kholia/HF-PA-v2/[Hans' Grounding + ESD Tip] Screenshot_2021-07-30_19-16-26.png

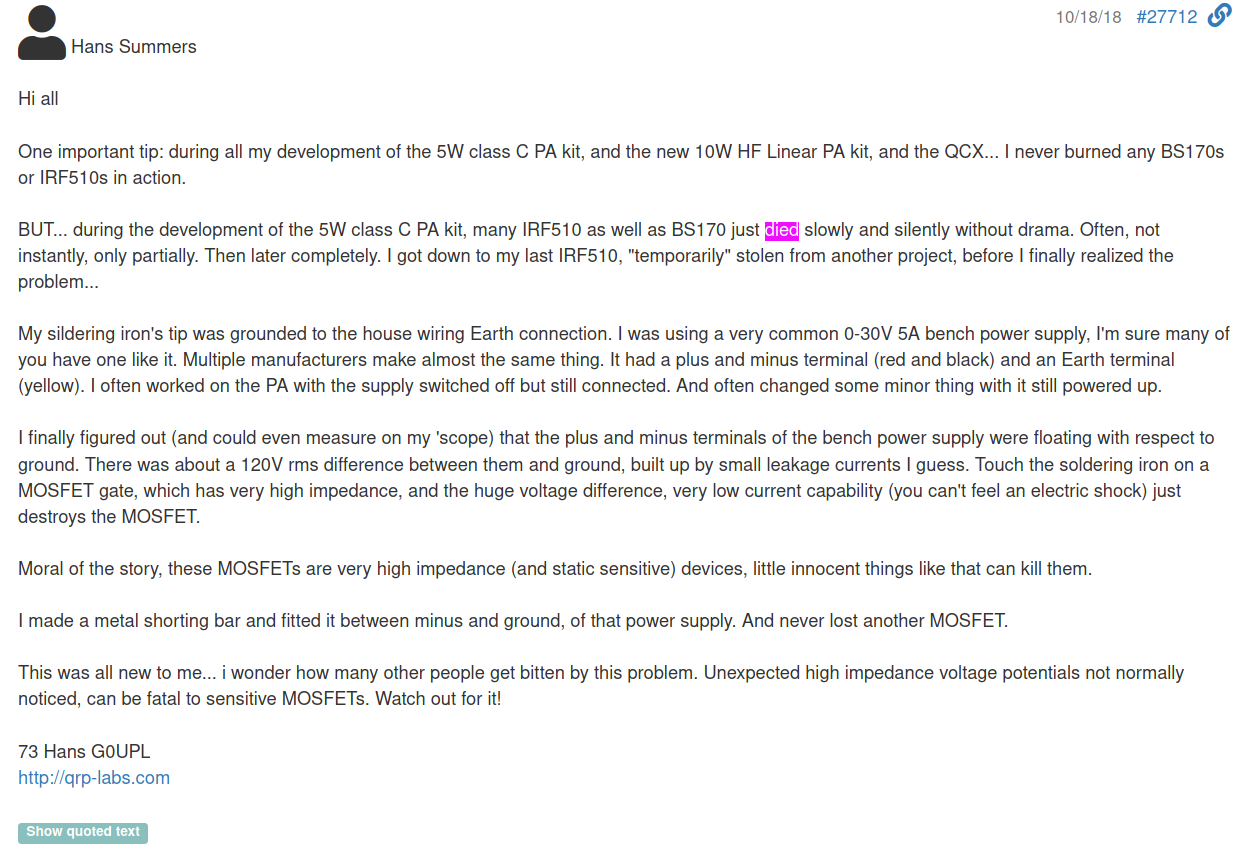
[Hans' Grounding + ESD Tip] Screenshot_2021-07-30_19-16-26.png
