kholia/HF-PA-v2/EWB-Power-Module-Robust-v3 - Screenshot_2021-07-06_10-33-40.png

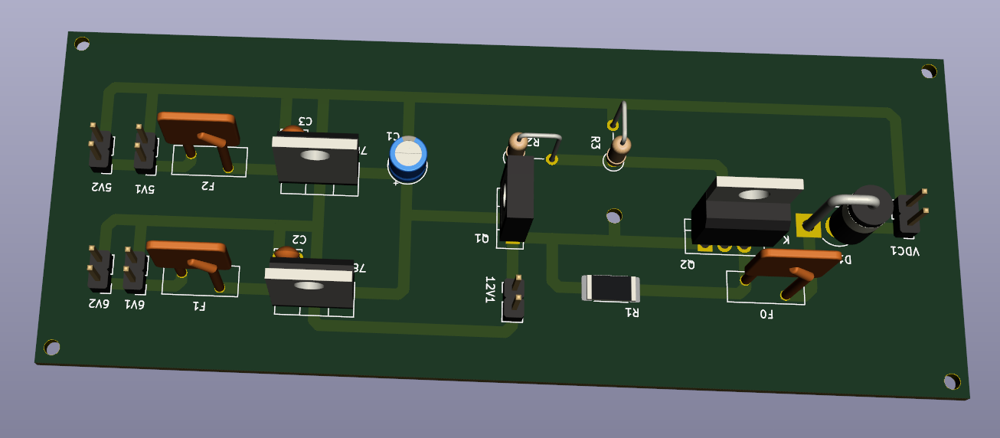
EWB-Power-Module-Robust-v3 - Screenshot_2021-07-06_10-33-40.png
