kholia/HF-PA-v2/HF-PA-Simulations/Screenshot_2021-07-11_12-03-48.png

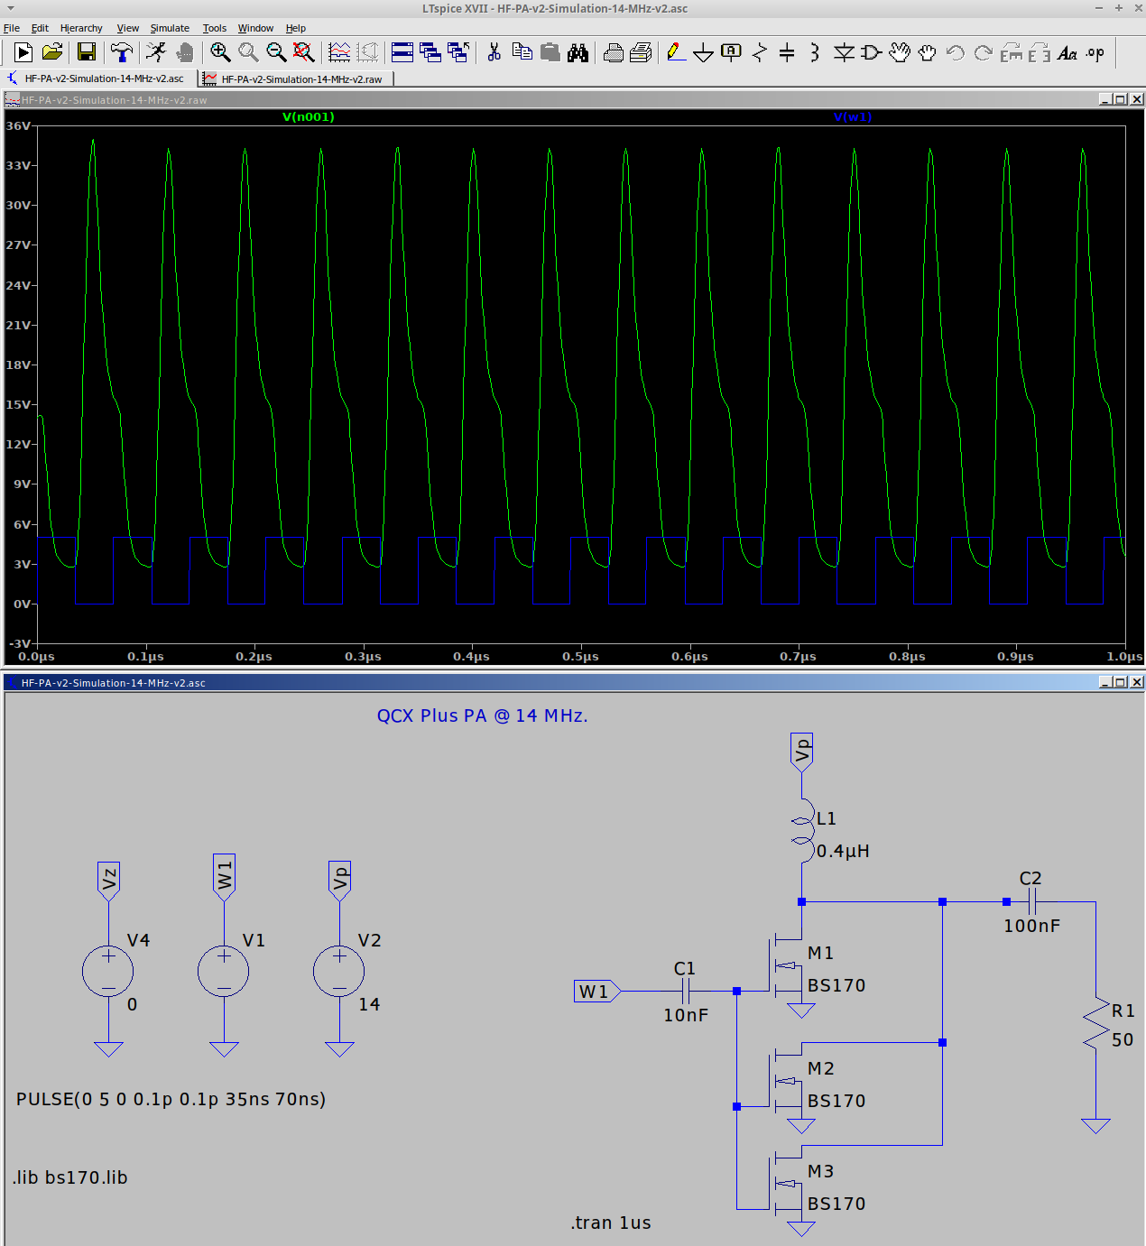
HF-PA-Simulations/Screenshot_2021-07-11_12-03-48.png
