kholia/HF-PA-v2/Images/v2-PCB/DS1054Z_DS1ZA203916662_2021-07-31_20.31.34.png

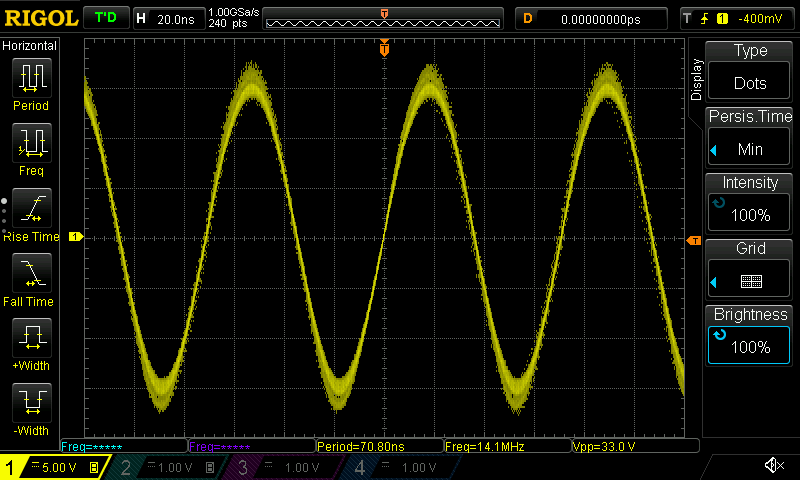
Images/v2-PCB/DS1054Z_DS1ZA203916662_2021-07-31_20.31.34.png
