kholia/HF-PA-v2/Info/20180319_120506-293x300.jpg

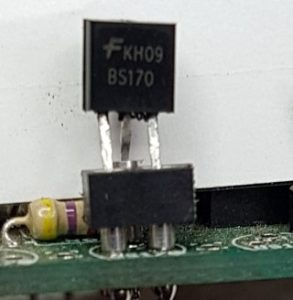
Info/20180319_120506-293x300.jpg
