kholia/HF-PA-v2/Info/DIP heatsink.jpg

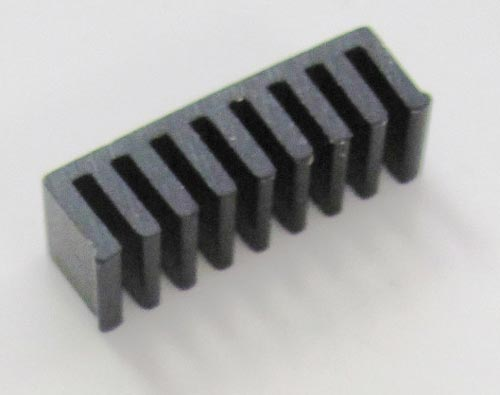
Info/DIP heatsink.jpg
