kholia/HF-PA-v2/Info/DIY Heat Sink Idea for BS170.jpeg

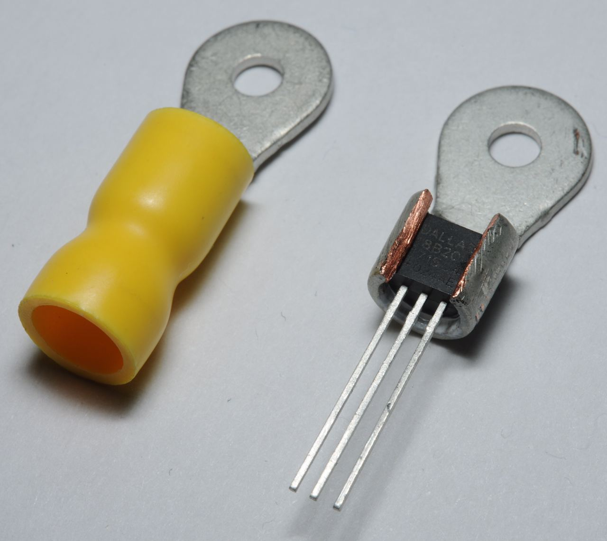
Info/DIY Heat Sink Idea for BS170.jpeg
