kholia/HF-PA-v2/Info/IMG_3917.jpg

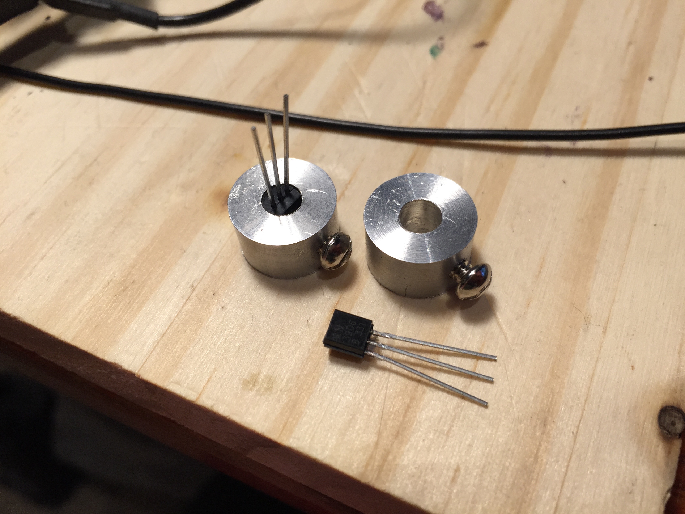
Info/IMG_3917.jpg
