kholia/HF-PA-v2/LPF Values - Screenshot_2021-03-08_13-37-28.png

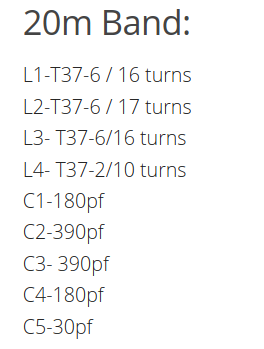
LPF Values - Screenshot_2021-03-08_13-37-28.png
