kholia/HF-PA-v2/Pretty-Close-Results-Screenshot_2021-07-26_19-14-53.png

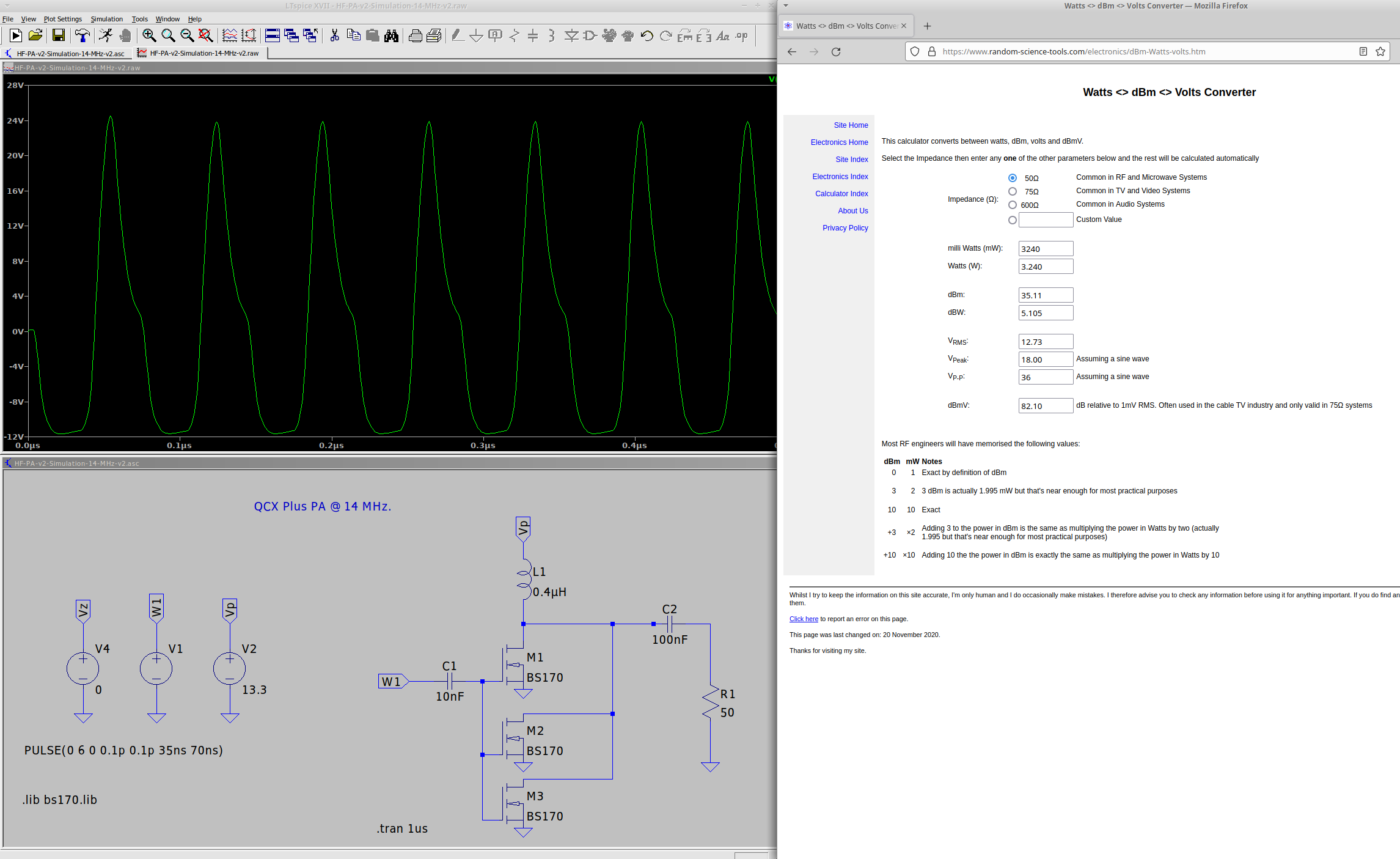
Pretty-Close-Results-Screenshot_2021-07-26_19-14-53.png
