kholia/HF-PA-v2/Current-Cutoff-Simulation/Current-Limiter-12v.asc

Q1: pnp; TIP42C
Q2: pnp; BD140
R1: res; 0.4
R2: res; {R}
R3: res; 1k
R4: res; 1k
U1: 7805
V1: voltage; 12.6
Named nets: 0
Current Limiting Circuit @ 12.6v
.inc TIP42C.LIB
.op
.step param R 1 10 0.5
