kholia/HF-PA-v2/HF-PA-Simulations/HF-PA-v2-Simulation-14-MHz-v2.asc

C1: cap; 10nF
C2: cap; 100nF
L1: ind; 0.4µH
M1: nmos; BS170
M2: nmos; BS170
M3: nmos; BS170
R1: res; 50
V1: voltage; PULSE(0 6 0 0.1p 0.1p 35ns 70ns)
V2: voltage; 13.8
V4: voltage; 0
Named nets: W1, 0, Vp, Vz
.tran 1us
QCX Plus PA @ 14 MHz.
.lib bs170.lib
